Raghav9git/ESP-32-IoT-PCB-Board-/Memory & Hierarchical Sheets.png

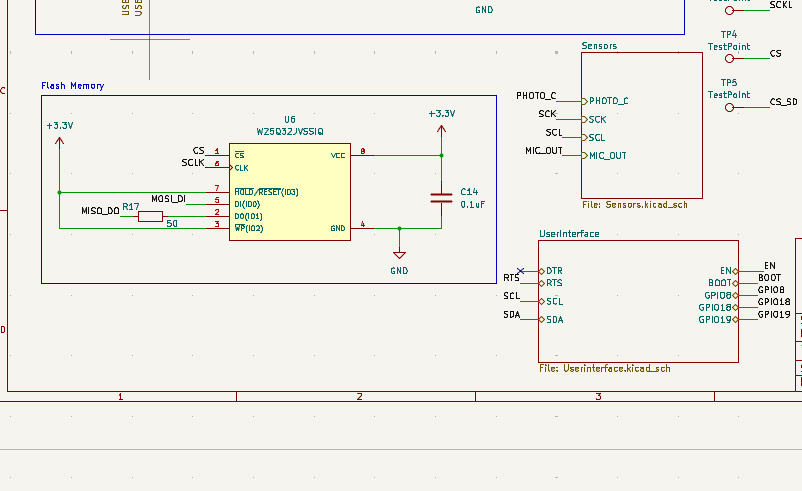
Memory & Hierarchical Sheets.png
