Raghav9git/ESP-32-IoT-PCB-Board-/Power Circuitry.png

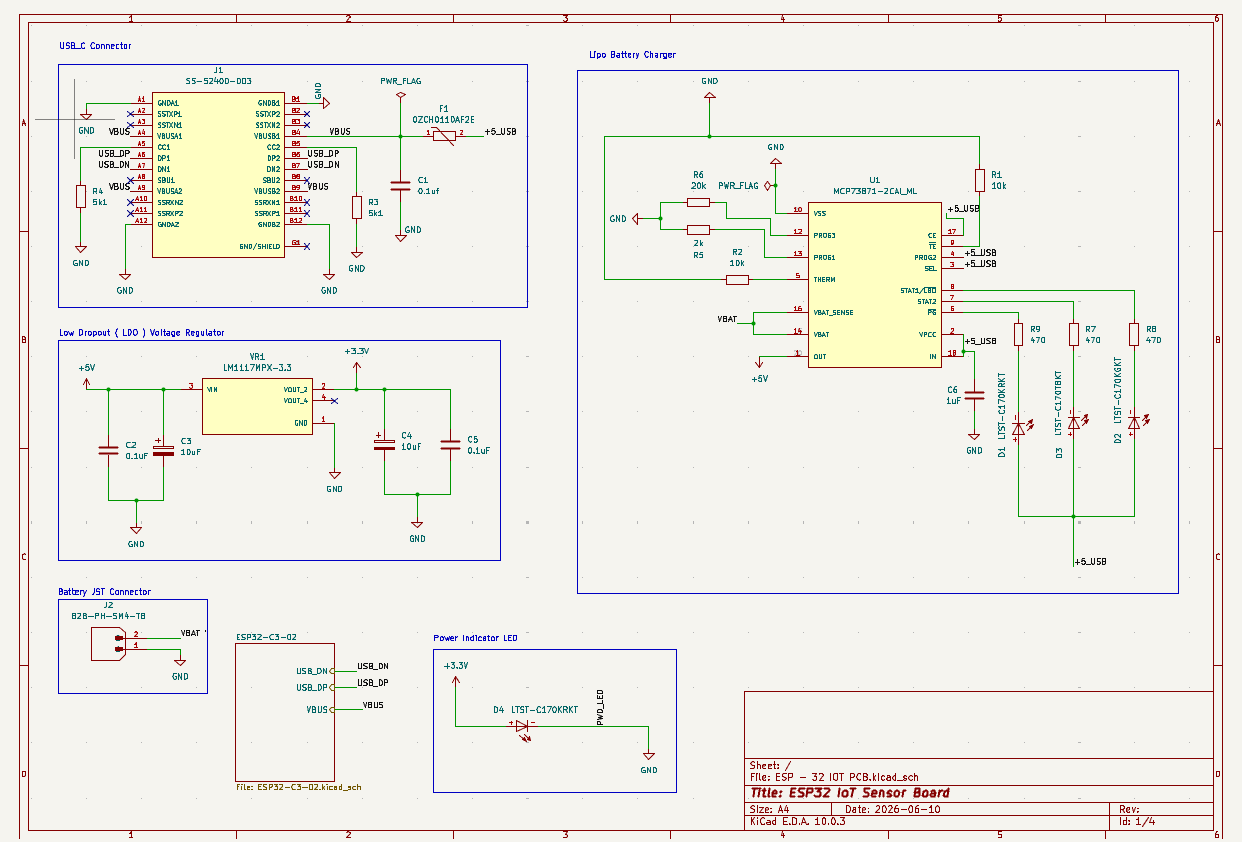
Power Circuitry.png
