Raghav9git/ESP-32-IoT-PCB-Board-/SD Card Module.png

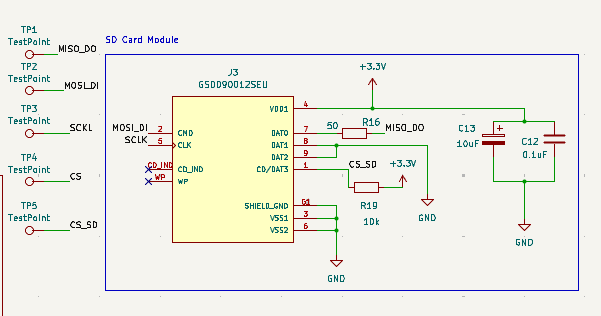
SD Card Module.png
